dubpixel/dpx_faded/hardware/spec/datasheet/1-APAI - SC1009M B10K 13T/apai_fader_drama/FROM_LYRIC_LOL/APAI - sc1009BM_LYRIC.png

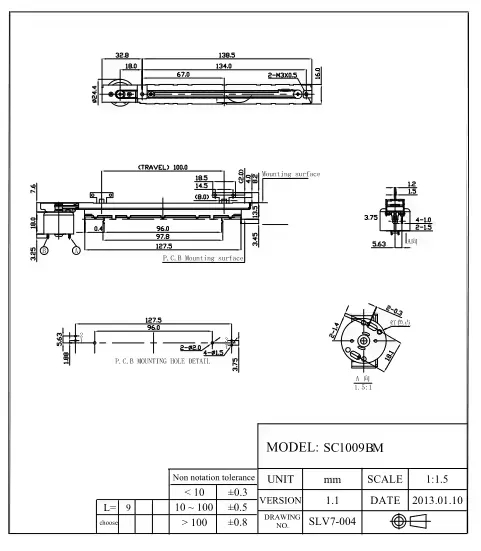
hardware/spec/datasheet/1-APAI - SC1009M B10K 13T/apai_fader_drama/FROM_LYRIC_LOL/APAI - sc1009BM_LYRIC.png
