dubpixel/dpx_faded/hardware/spec/datasheet/1-APAI - SC1009M B10K 13T/Circuit_only_diagram.png

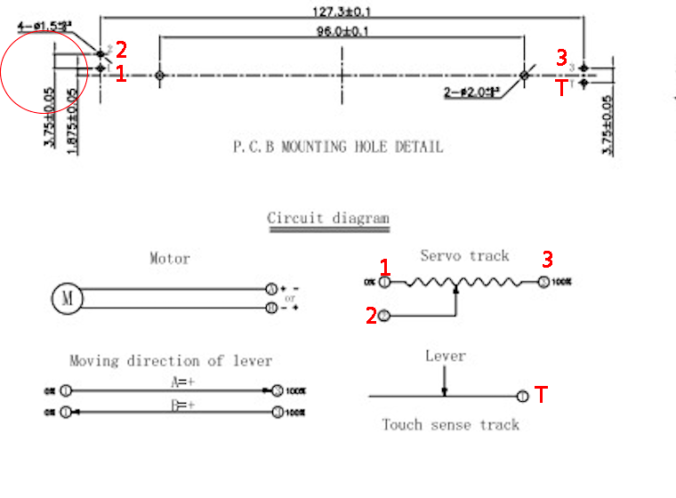
hardware/spec/datasheet/1-APAI - SC1009M B10K 13T/Circuit_only_diagram.png
