dubpixel/dpx_faded/hardware/spec/datasheet/1-APAI - SC1009M B10K 13T/fader_apai_SC1009M_.png

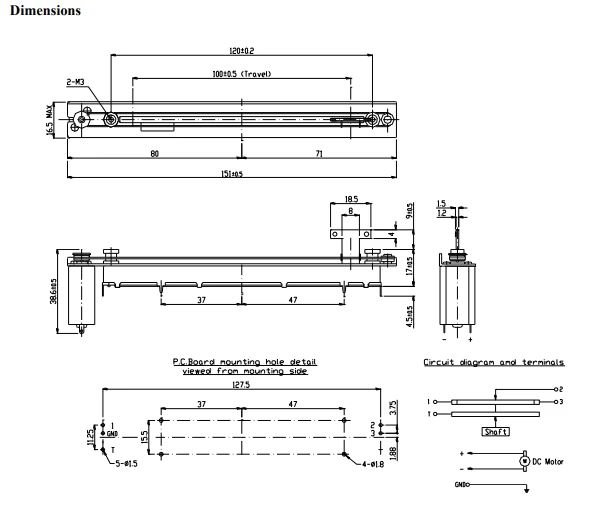
hardware/spec/datasheet/1-APAI - SC1009M B10K 13T/fader_apai_SC1009M_.png
