dubpixel/dpx_faded/hardware/spec/datasheet/2-TERWIN/sm100N-b10k-l8.2T-DF/SM100N-B10K-L8.2T-DF.webp

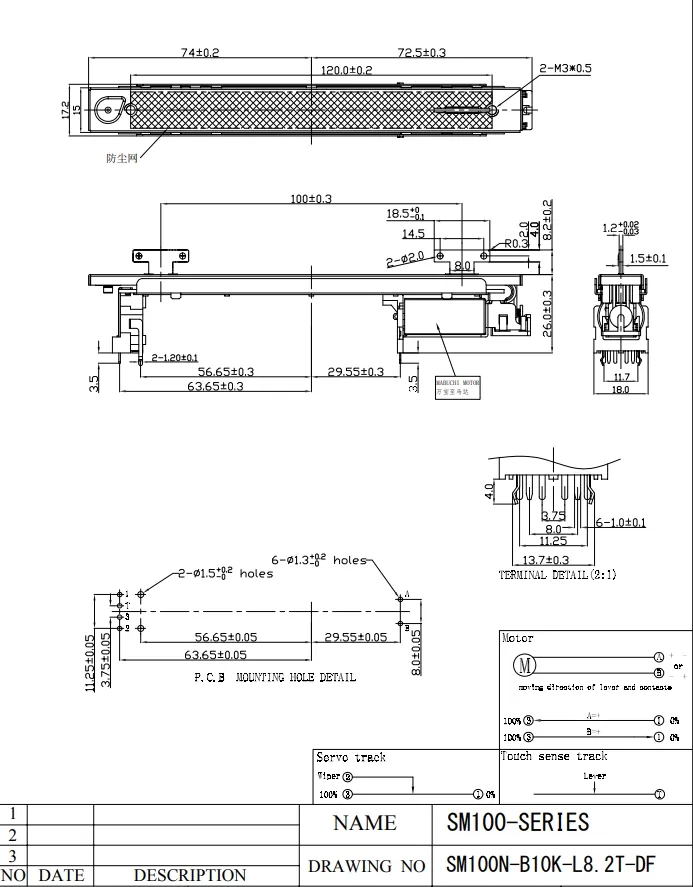
hardware/spec/datasheet/2-TERWIN/sm100N-b10k-l8.2T-DF/SM100N-B10K-L8.2T-DF.webp
