dubpixel/dpx_faded/hardware/spec/datasheet/2-TERWIN/terwin_100mm_10k_what _they_sent_h4.png

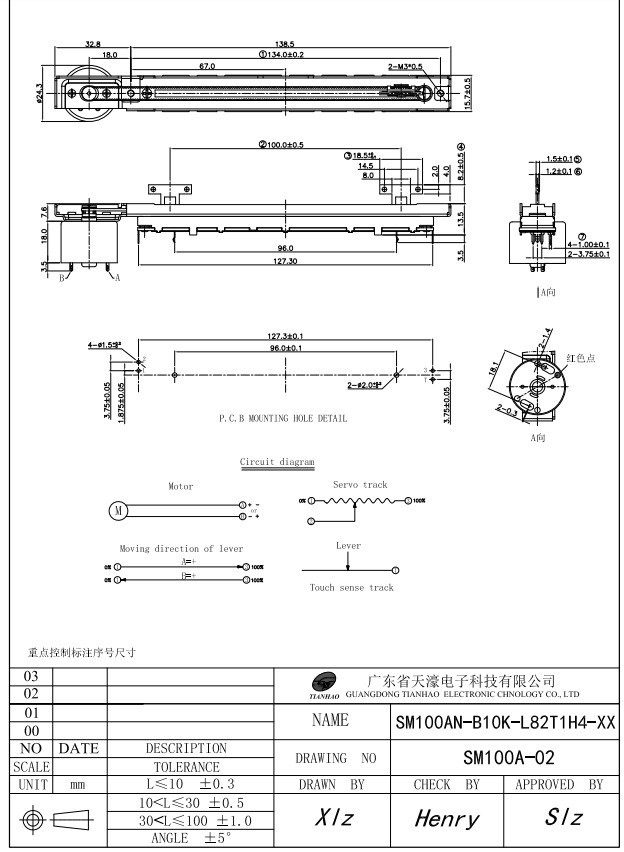
hardware/spec/datasheet/2-TERWIN/terwin_100mm_10k_what _they_sent_h4.png
