dubpixel/dpx_faded/hardware/spec/datasheet/2-TERWIN/terwin_100mm_10k_what_i _wanted_h5.png

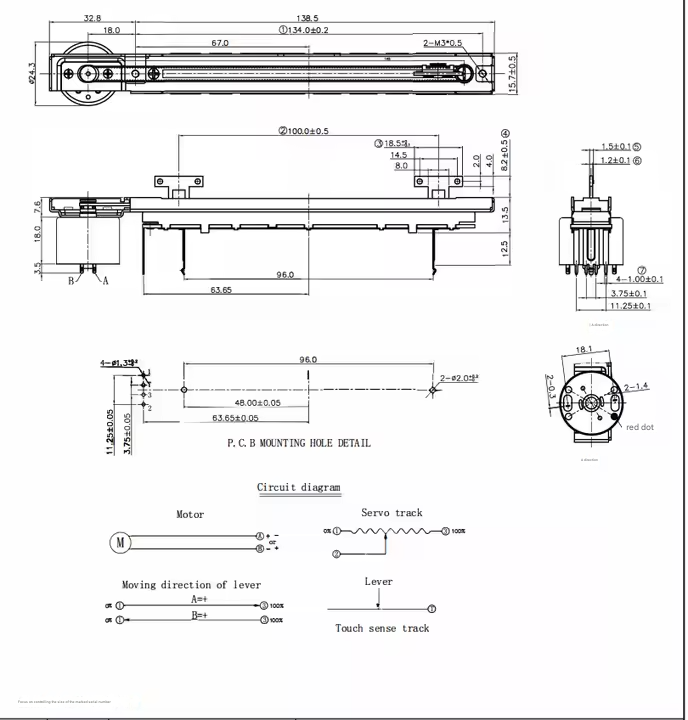
hardware/spec/datasheet/2-TERWIN/terwin_100mm_10k_what_i _wanted_h5.png
