dubpixel/dpx_faded/hardware/spec/datasheet/2-TERWIN/terwin_another_compact_pcbmotor.webp

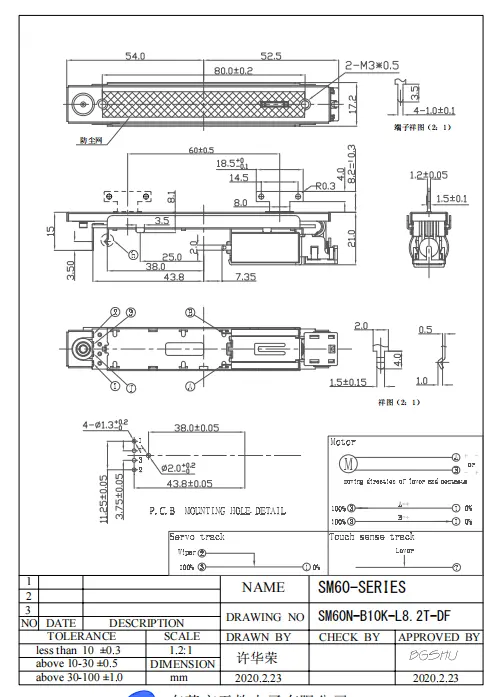
hardware/spec/datasheet/2-TERWIN/terwin_another_compact_pcbmotor.webp
