dubpixel/dpx_faded/hardware/spec/datasheet/3-terwinx32/terwin_x32.png

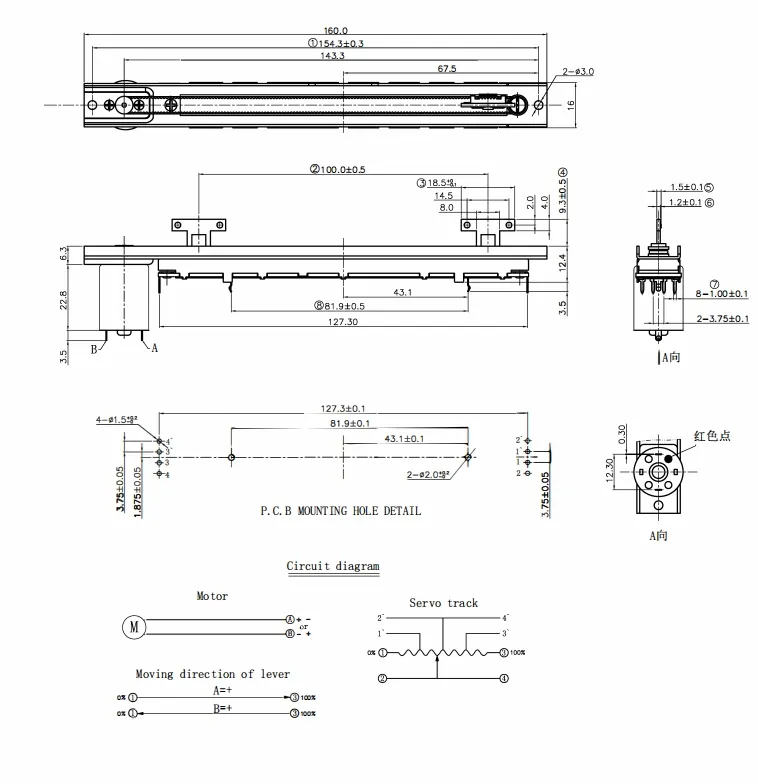
hardware/spec/datasheet/3-terwinx32/terwin_x32.png
