dubpixel/dpx_faded/hardware/spec/datasheet/photos_of_things/x32_behringer_fader_rev.jpeg

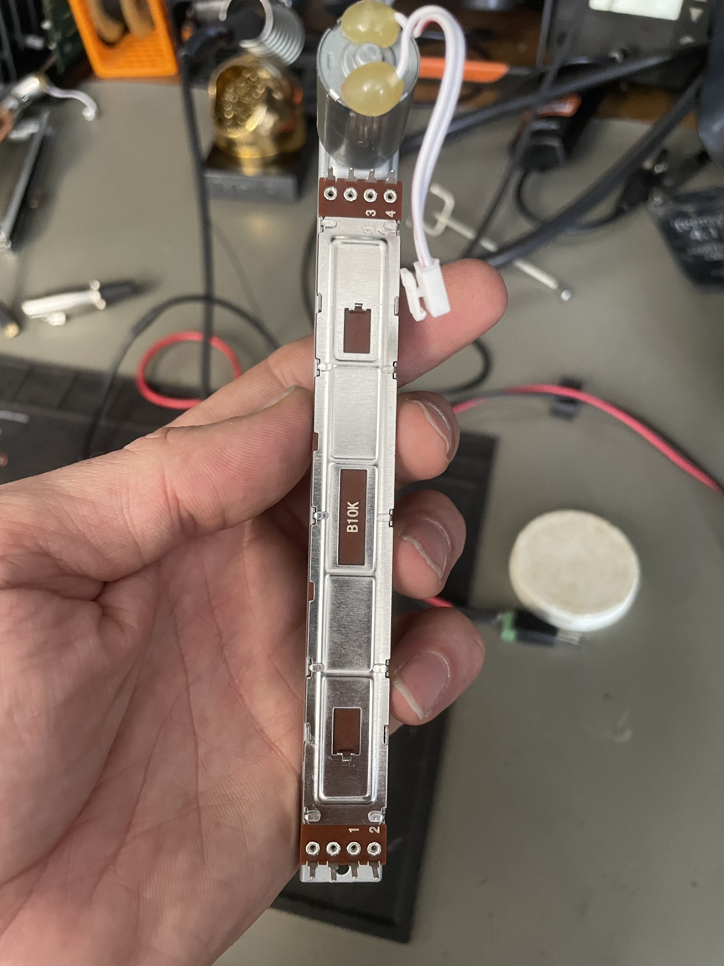
hardware/spec/datasheet/photos_of_things/x32_behringer_fader_rev.jpeg
