dubpixel/dpx_faded/hardware/spec/datasheet/PINOUT_COMPARISONS/IDEAL_PINOUT_FROM_FADE4.png

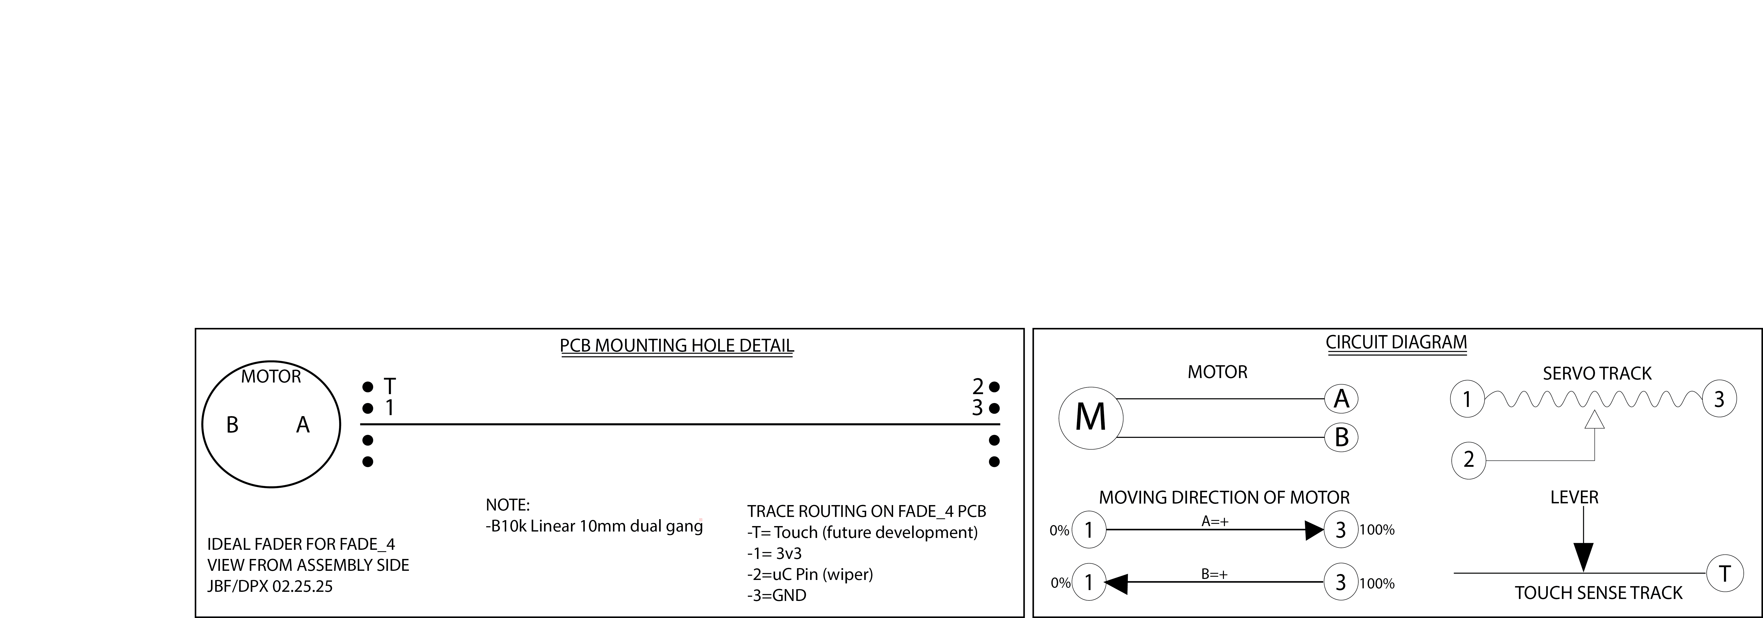
hardware/spec/datasheet/PINOUT_COMPARISONS/IDEAL_PINOUT_FROM_FADE4.png
