dubpixel/dpx_faded/hardware/spec/datasheet/x32_pot_symbol.png

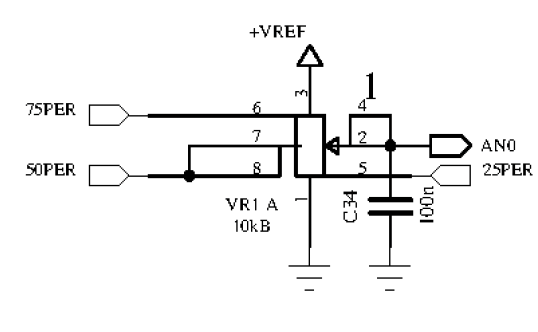
hardware/spec/datasheet/x32_pot_symbol.png
