dubpixel/dpx_faded/hardware/spec/datasheet/photos_of_things/fade4_pcb.jpeg

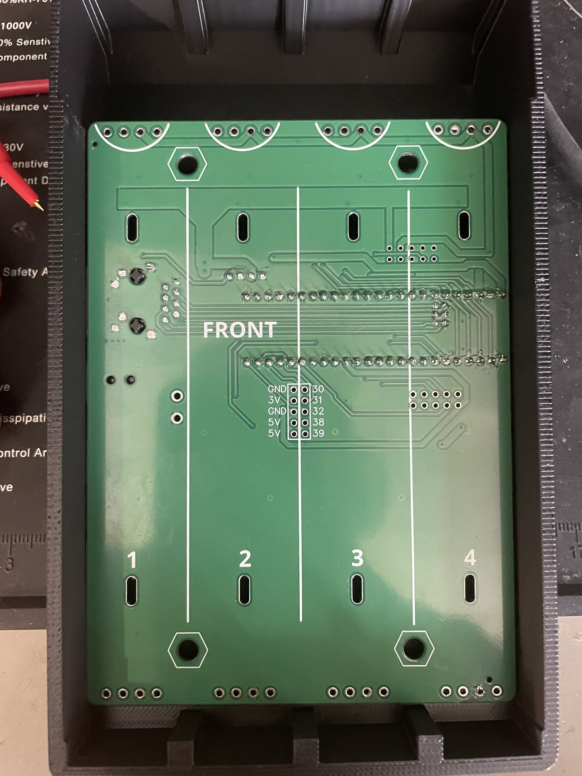
hardware/spec/datasheet/photos_of_things/fade4_pcb.jpeg
